tonyechen/TECHIN_512_Final/Documentation/Controller.kicad_sch

## KiCad design Documentation/Controller.kicad_sch (2025-12-03)

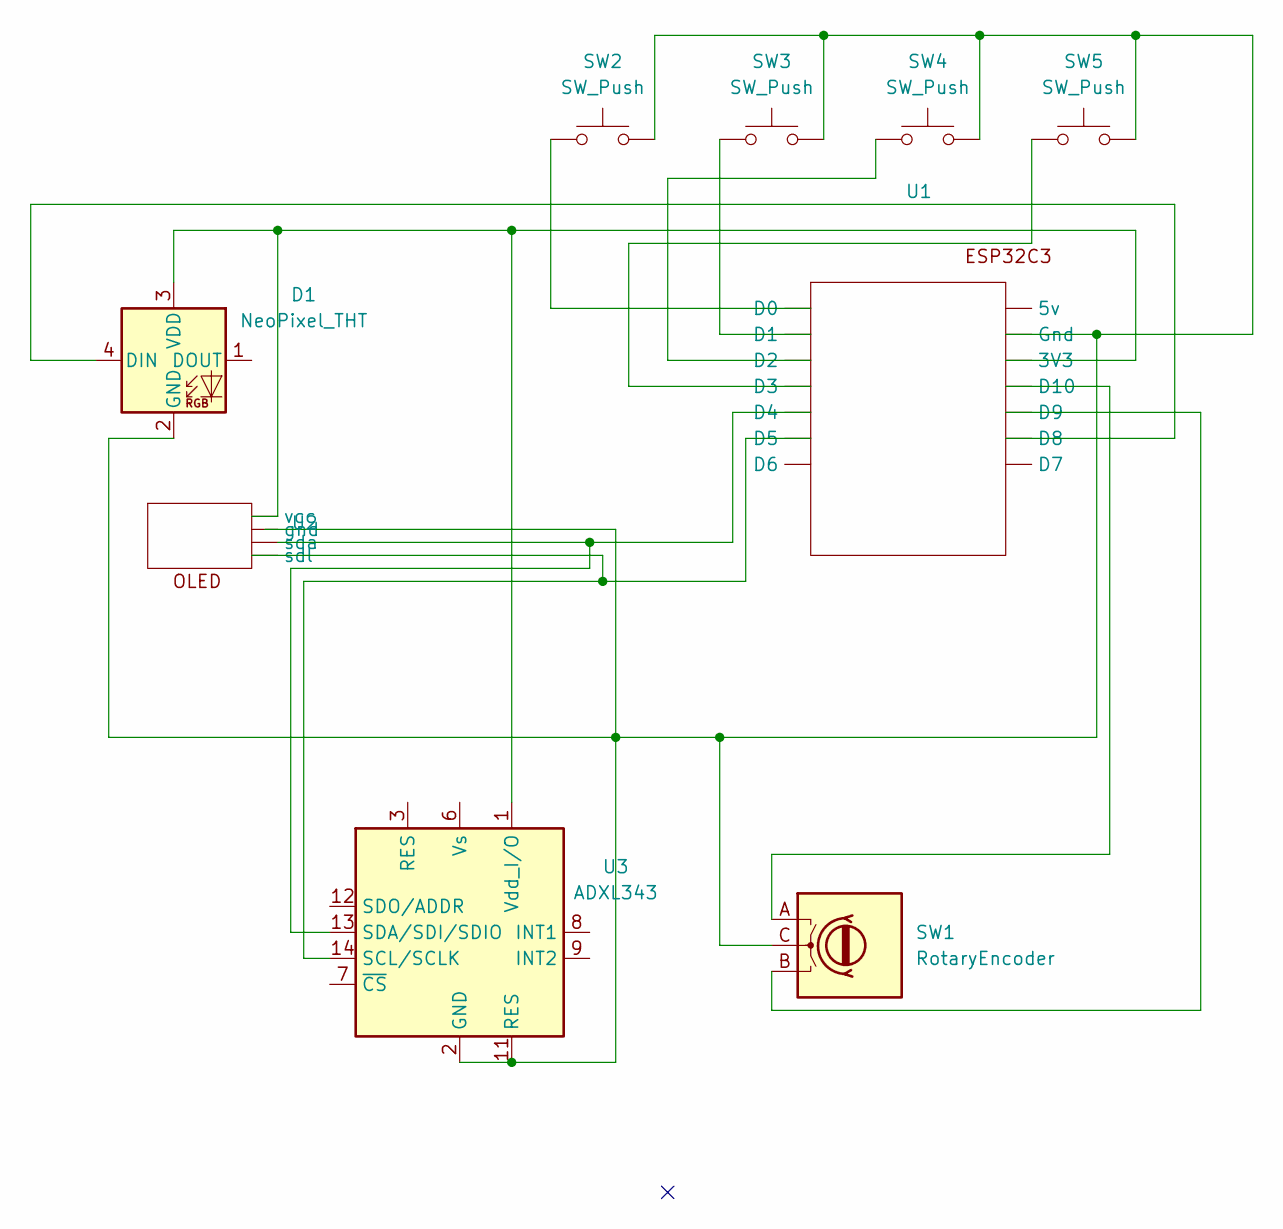
[picture p2: schematic Controller.kicad_sch]

Parts:
D1: NeoPixel_THT
SW1: RotaryEncoder
SW2, SW3, SW4, SW5: SW_Push
U1, U2: (no value)
U3: ADXL343; LGA-14_3x5mm_P0.8mm_LayoutBorder1x6y

Connections:
unnamed: D1.2 (GND), SW1.C, SW2.2, SW3.2, SW4.2, SW5.2, U1., U3.2 (GND), U3.4 (GND), U3.5 (GND), U3.11 (RES)
unnamed: D1.3 (VDD), U1., U2., U3.1 (Vdd_I/O)
unnamed: D1.4 (DIN), U1.
unnamed: SW1.A, U1.
unnamed: SW1.B, U1.
unnamed: SW2.1, U1.
unnamed: SW3.1, U1.
unnamed: SW4.1, U1.
unnamed: SW5.1, U1.
unnamed: U1., U2., U3.13 (SDA/SDI/SDIO), U3.14 (SCL/SCLK)
