tonyechen/TECHIN_512_Final/Documentation/Srappy.kicad_sch

## KiCad design Documentation/Srappy.kicad_sch (2025-12-10)

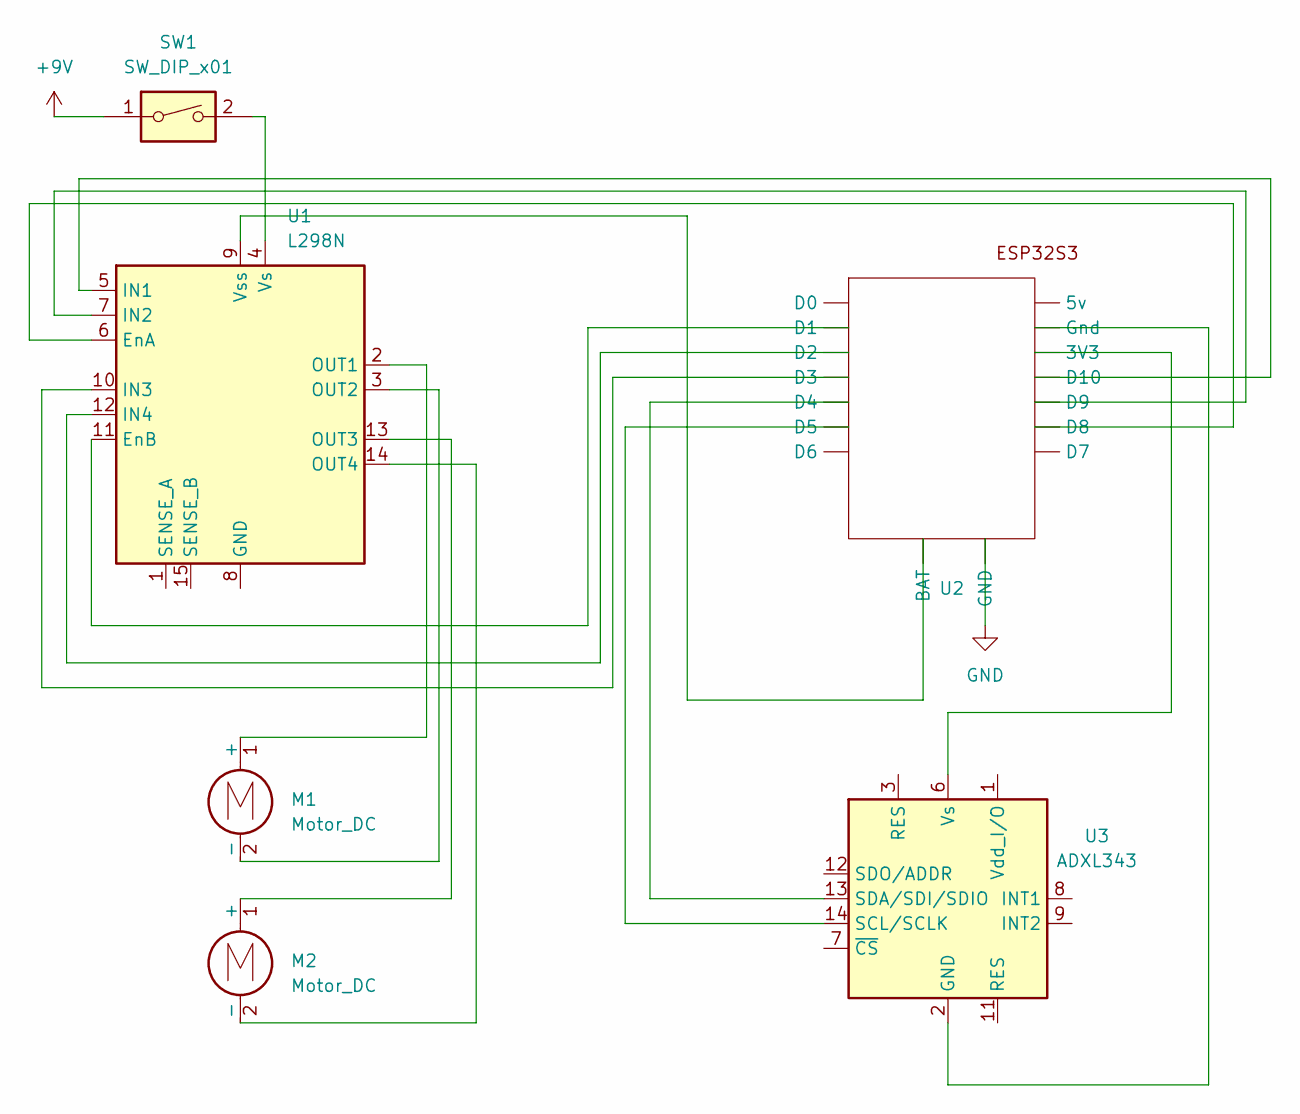
[picture p3: schematic Srappy.kicad_sch]

Parts:
M1, M2: Motor_DC
SW1: SW_DIP_x01
U1: L298N; TO-220-15_P2.54x5.08mm_StaggerOdd_Lead4.58mm_Vertical
U2: (no value)
U3: ADXL343; LGA-14_3x5mm_P0.8mm_LayoutBorder1x6y

Connections:
+9V: SW1.1
GND: U2.
unnamed: M1.1 (+), U1.2 (OUT1)
unnamed: M1.2 (-), U1.3 (OUT2)
unnamed: M2.1 (+), U1.13 (OUT3)
unnamed: M2.2 (-), U1.14 (OUT4)
unnamed: SW1.2, U1.4 (Vs)
unnamed: U1.5 (IN1), U2.
unnamed: U1.6 (EnA), U2.
unnamed: U1.7 (IN2), U2.
unnamed: U1.9 (Vss), U2.
unnamed: U1.10 (IN3), U2.
unnamed: U1.11 (EnB), U2.
unnamed: U1.12 (IN4), U2.
unnamed: U2., U3.2 (GND), U3.4 (GND), U3.5 (GND), U3.6 (Vs), U3.13 (SDA/SDI/SDIO), U3.14 (SCL/SCLK)
